davidgilson/Hexagonal-Power-Bank/images/01.jpg

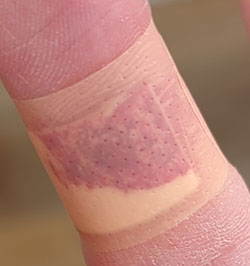
images/01.jpg
