davidgilson/Hexagonal-Power-Bank/images/09.jpg

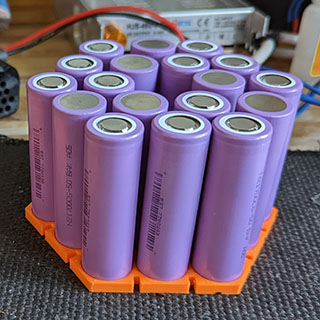
images/09.jpg
