davidgilson/Hexagonal-Power-Bank/STL/case-FINAL.stl

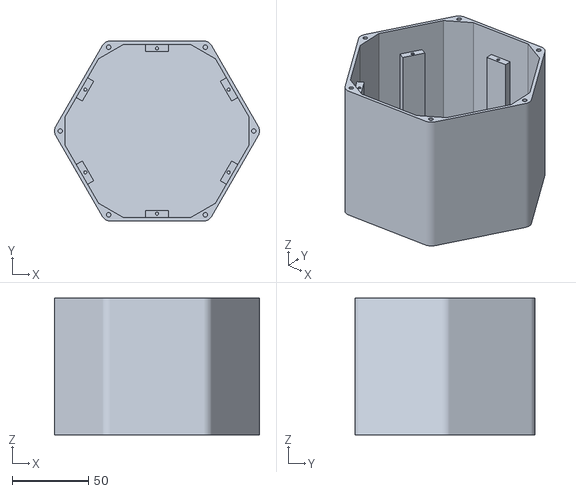
[picture p60: CAD file, 2022-08-06]
STL/case-FINAL.stl
134.8 x 118.4 x 90.0
