davidgilson/Hexagonal-Power-Bank/STL/wireless-logo.stl

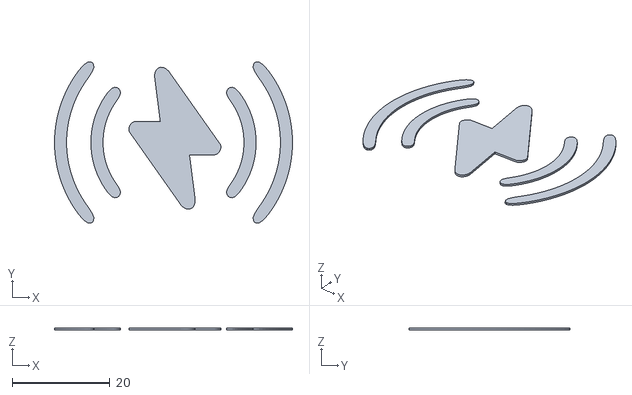
[picture p61: CAD file, 2022-08-06]
STL/wireless-logo.stl
48.7 x 33.0 x 0.4
