davidgilson/Hexagonal-Power-Bank/STL/Meter Holder.stl

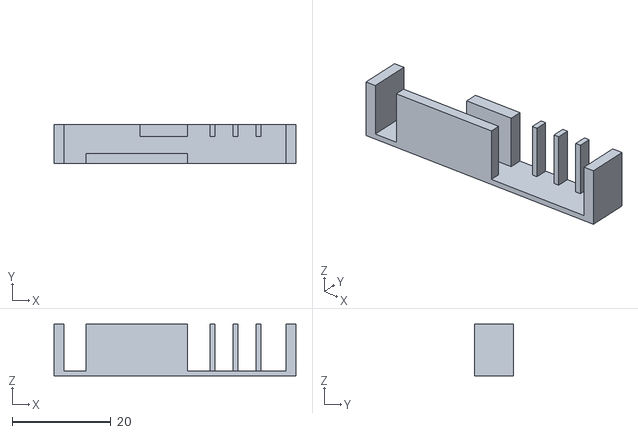
[picture p62: CAD file, 2022-08-06]
STL/Meter Holder.stl
49.0 x 7.89 x 10.5
